adam-ctrlc/sigurado/paper/figures/web-flags.png

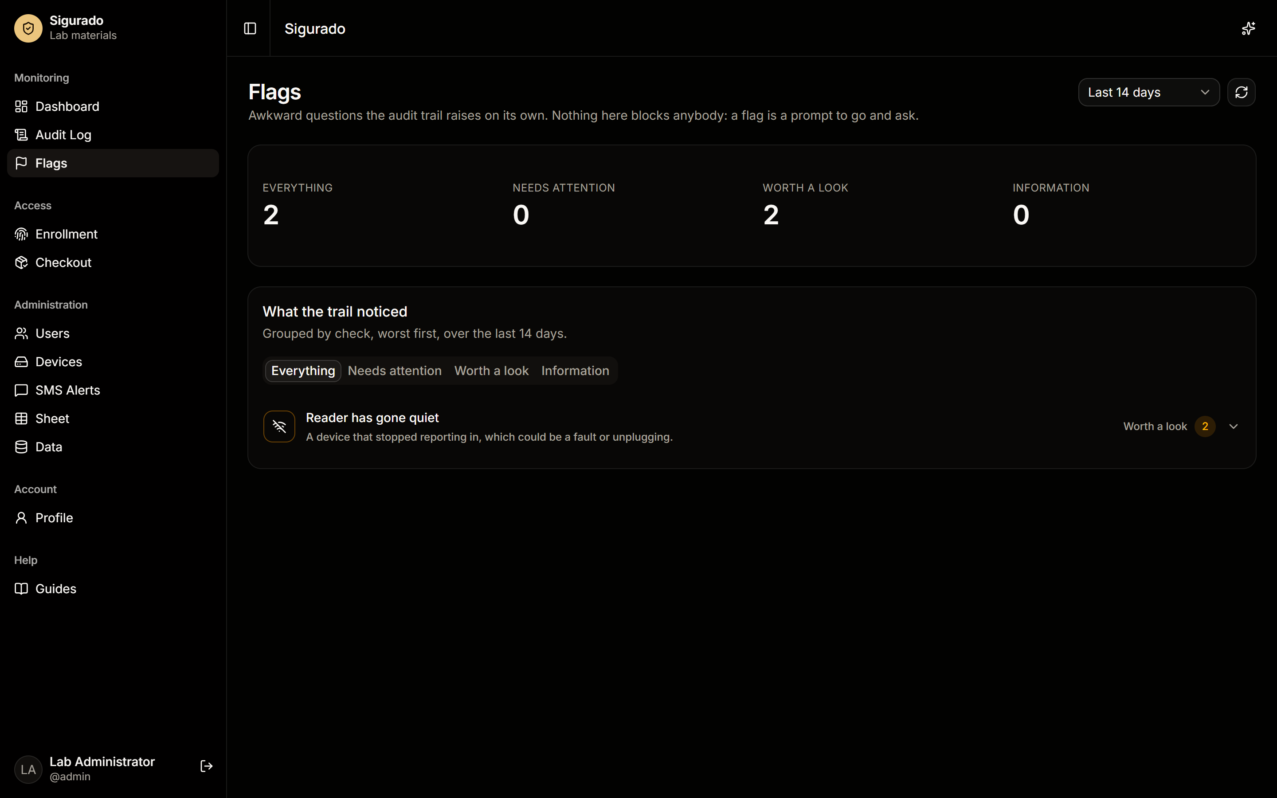
paper/figures/web-flags.png
