adam-ctrlc/sigurado/paper/figures/web-login.png

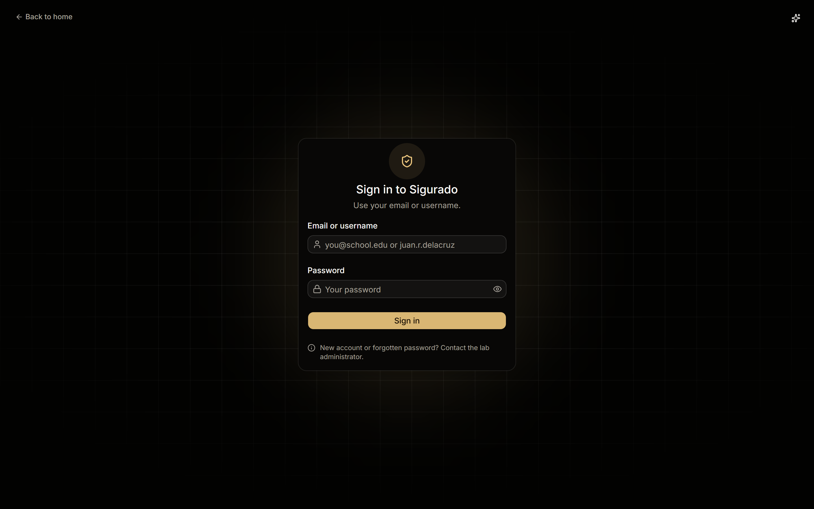
paper/figures/web-login.png
