adam-ctrlc/sigurado/backend/src/error.rs

use axum::{
    Json,
    http::StatusCode,
    response::{IntoResponse, Response},
};
use serde_json::json;

pub type AppResult<T> = Result<T, AppError>;

#[derive(Debug, thiserror::Error)]
pub enum AppError {
    #[error("authentication required")]
    Unauthorized,
    #[error("you do not have access to this resource")]
    Forbidden,
    #[error("{0} not found")]
    NotFound(&'static str),
    #[error("{0}")]
    Conflict(String),
    #[error("{0}")]
    Validation(String),
    #[error("{0}")]
    BadRequest(String),
    #[error(transparent)]
    Db(#[from] sea_orm::DbErr),
    #[error(transparent)]
    Internal(#[from] anyhow::Error),
}

impl AppError {
    fn parts(&self) -> (StatusCode, &'static str) {
        match self {
            Self::Unauthorized => (StatusCode::UNAUTHORIZED, "unauthorized"),
            Self::Forbidden => (StatusCode::FORBIDDEN, "forbidden"),
            Self::NotFound(_) => (StatusCode::NOT_FOUND, "not_found"),
            Self::Conflict(_) => (StatusCode::CONFLICT, "conflict"),
            Self::Validation(_) => (StatusCode::UNPROCESSABLE_ENTITY, "validation"),
            Self::BadRequest(_) => (StatusCode::BAD_REQUEST, "bad_request"),
            Self::Db(_) | Self::Internal(_) => (StatusCode::INTERNAL_SERVER_ERROR, "internal"),
        }
    }
}

impl IntoResponse for AppError {
    fn into_response(self) -> Response {
        let (status, code) = self.parts();
        if status == StatusCode::INTERNAL_SERVER_ERROR {
            tracing::error!(error = %self, "request failed");
        }
        let message = match &self {
            Self::Db(_) | Self::Internal(_) => "an internal error occurred".to_owned(),
            other => other.to_string(),
        };
        let body = Json(json!({ "error": { "code": code, "message": message } }));
        (status, body).into_response()
    }
}
